jgOhYeah/BikeHorn/Documentation/Images/PCB_Front.jpg

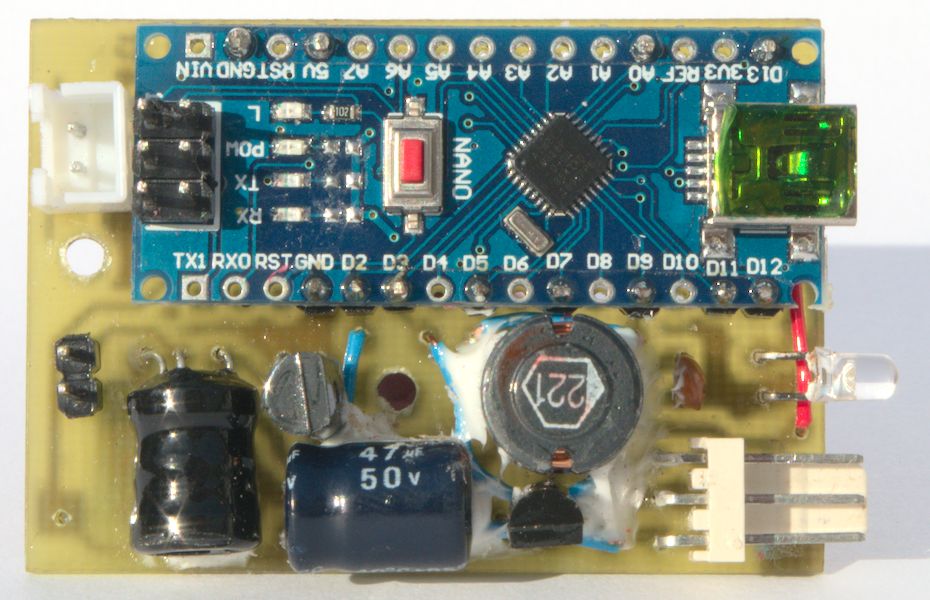
Documentation/Images/PCB_Front.jpg
