jgOhYeah/BikeHorn/Tuning/OptimiserSketch/OptimiserSketch.ino

/**
 * @file OptimiserSketch.ino
 * @author Jotham Gates
 * @brief Sketch for use with the BikeHornOptimiser tool for tuning the horn to get best performance
 * @date 2021-12-30
 * 
 * Upload this sketch to the horn and run BikeHornOptimiser.py.
 * NOTE: This script DOES NOT include any low power features. When you are finished, either remove
 * the batteries or reflash the proper BikeHorn sketch (that does have power saving features),
 * otherwise you will end up with flat batteries.
 */

#include <EEPROM.h>
#include <stdio.h>

#define PIEZO_PIN 9 // Fixed as PB1 (Pin 9 on Arduino Nano)
#define BOOST_PIN 11 // Fixed as PB3 (Pin 11 on Arduino Nano)
#define LED_EXTERNAL 7
#define SERIAL_BAUD 38400

#define VERSION "1.0.0"
#define WELCOME_MSG "Bike horn OPTIMISER V" VERSION " started. Compiled " __TIME__ ", " __DATE__

static FILE uartout = {0}; // https://playground.arduino.cc/Main/Printf/

/**
 * @brief Initial setup and signalling to the computer
 * 
 */
void setup() {
    // Fprintf stuff
    // Fill in the UART file descriptor with pointer to writer.
    fdev_setup_stream (&uartout, uart_putchar, NULL, _FDEV_SETUP_WRITE);
    // The uart is the standard output device STDOUT.
    stdout = &uartout ;

    // Initial setup
    Serial.begin(SERIAL_BAUD);
    Serial.setTimeout(__LONG_MAX__);
    pinMode(LED_BUILTIN, OUTPUT);
    pinMode(LED_EXTERNAL, OUTPUT);
    pinMode(PIEZO_PIN, OUTPUT);
    pinMode(BOOST_PIN, OUTPUT);
    digitalWrite(LED_BUILTIN, HIGH);
    digitalWrite(LED_EXTERNAL, HIGH);
    Serial.println(F(WELCOME_MSG));

    // Wait for the computer
    Serial.println(F("~`~`Ready`~`~"));
}

/**
 * @brief Main program loop
 * 
 */
void loop() {
    // Wait for the start of the message
    digitalWrite(LED_EXTERNAL, HIGH);
    Serial.find("~`~`");
    while(!Serial.available());
    char instruction = Serial.read();
    digitalWrite(LED_EXTERNAL, LOW);

    bool simpleAck = true;

    // Tune playing settings
    uint16_t t1Top, t1Compare;
    uint8_t t2Compare;

    // Interpret the instruction
    switch(instruction) {
        case 'p':
            // Play a note
            t1Top = Serial.parseInt();
            Serial.find('~');
            t1Compare = Serial.parseInt();
            Serial.find('~');
            t2Compare = Serial.parseInt();

            playNote(t1Top, t1Compare, t2Compare);
            break;
        case 's':
            // Stop all timers and noise
            stop();
            break;
        case 'w':
            // Write a eeprom bytes
            writeStream();
            simpleAck = false;
            break;
        case 'r':
            // Read the specified number of eeprom bytes from an address
            dumpEEPROM();
            
    }

    // Acknowledge
    if(simpleAck) {
        // Wait for the end of the message
        Serial.find("`~`~");
        Serial.println(F("~`~`Ack`~`~"));
    }
}

/**
 * @brief Sets up the timers to play with the given parameters
 * 
 * @param t1Top timer 1 top, to be put in ICR1
 * @param t1Compare timer 1 compare, to be put in OCR1A
 * @param t2Compare timer 2 compare, to be put in OCR2A (top is fixed at 0xff)
 */
void playNote(uint16_t t1Top, uint16_t t1Compare, uint8_t t2Compare) {
    // Setup non inverting mode (duty cycle is sensible), fast pwm mode 14 on PB1 (Pin 9)
    TCCR1A = (1 << COM1A1) | (1 << WGM11);
    TCCR1B = (1 << WGM12) | (1 << WGM13) | (1 << CS11); // With prescalar 8 (with a clock frequency of 16MHz, can get all notes required)
    ICR1 = t1Top; // Calculate the corresponding counter
    OCR1A = t1Compare; // Duty cycle

    TCCR2A = (1 << COM2A1) | (1 << WGM21) | (1 << WGM20); // Mode 3, fast PWM, reset at 255
    TCCR2B = (1<< CS20); // Prescalar 1
    OCR2A = t2Compare; // Duty cycle
}

/**
 * @brief Shuts down the timers and stops making noise
 * 
 */
void stop() {
    TCCR1A = 0;
    TCCR1B = 0;
    TCCR2A = 0;
    TCCR2B = 0;

    digitalWrite(BOOST_PIN, LOW);
    digitalWrite(PIEZO_PIN, LOW);
}

void writeStream() {
    uint16_t address = Serial.parseInt();
    bool done = false;
    while(!done) {
        char input = waitByte();
        if(input == '~') {
            // Get and write a byte
            uint8_t data = Serial.parseInt();
            EEPROM.update(address, data);
            address++;
            Serial.println(F("~`~`W`~`~"));
        } else if(input == '`') {
            input = waitByte();
            if(input == '~') {
                input = waitByte();
                if(input == '`') {
                    input = waitByte();
                    if(input == '~') {
                        done = true;
                    }
                }
            }
        }
    }
    Serial.println(F("~`~`Ack`~`~"));
}

char waitByte() {
    while(!Serial.available()) {}
    return Serial.read();
}


void dumpEEPROM() {
    const char WIDTH = 16;
    const int EEPROM_SIZE = 1024;

    // Header row
    printf("     | ");
    for(int i = 0; i < WIDTH; i++) {
        printf("%02X ", i);
    }
    printf("\n");
    for(int i = 0; i < WIDTH*3+7; i++) {
        printf("-", i);
    }

    // Body
    for(int i = 0; i < EEPROM_SIZE; i += WIDTH) {
        printf("\n%04X | ", i);
        // Row
        for(int j = 0; j < WIDTH; j++) {
            printf("%02X ", EEPROM.read(i+j));
        }
    }
    printf("\n");
}

/**
 * @brief output function for printf
 * From https://playground.arduino.cc/Main/Printf/
 * 
 */
static int uart_putchar (char c, FILE *stream) {
    Serial.write(c) ;
    return 0 ;
}
