jgOhYeah/BikeHorn/BikeHorn/tunes.h

/** tunes.h
 * Saved tunes for the BikeHorn to play. Add each tune as an array, then edit
 * the tunes array at the bottom to include the name of the tune.
 * 
 * For more details, see README.md or go to
 * https://github.com/jgOhYeah/BikeHorn
 * 
 * Written by Jotham Gates. Tunes converted from various sources.
 * Last modified 11/01/2021
 */
#pragma once

// Converted from 'WeWishYouAMerryChristmas' by TunePlayer Musescore plugin V1.8.0
const uint16_t WeWishYouAMerryChristmas[] PROGMEM = {
    0xe0c8, // Tempo change to 200 BPM
    0x6a38,0xba38,0xba18,0x1c18,0xba18,0xaa18,0x8a38,0x8a38,0x8a38,0x1c38,
    0x1c18,0x3c18,0x1c18,0xba18,0xaa38,0x6a38,0x6a38,0x3c38,0x3c18,0x4c18,
    0x3c18,0x1c18,0xba38,0x8a38,0x6a18,0x6a18,0x8a38,0x1c38,0xaa38,0xba78,
    0x6a38,0xba18,0xaa18,0x8a18,0xaa18,0xba18,0x8a18,0xaa78,0xaa38,0xba38,
    0xaa38,0x8a38,0x6a78,0x1c38,0x3c38,0x1c18,0x1c18,0xba18,0xba18,0x6c38,
    0x6a38,0x6a18,0x6a18,0x8a38,0x1c38,0xaa38,0xba0c,0xaa0c,0xba0c,0xaa0c,
    0xba38,
    0xf001 // End of tune. Restart from the beginning.
};

// Converted from 'auld_lang_syne_PNO_orig' by TunePlayer Musescore plugin V1.8.0
const uint16_t auld_lang_syne_PNO_orig[] PROGMEM = {
    0xe0dc, // Tempo change to 220 BPM
    0x9a38,0x2c58,0x2c18,0x2c38,0x6c38,0x4c58,0x2c18,0x4c38,0x6c38,0x2c58,
    0x2c18,0x6c38,0x9c38,0xbcb8,0xbc38,0x9c58,0x6c18,0x6c38,0x2c38,0x4c58,
    0x2c18,0x4c38,0x6c38,0x2c58,0xba18,0xba38,0x9a38,0x2cb8,0xbc38,0x9c58,
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
    0x7a38,0x2a18,0x7a38,0x2a38,0x1a18,0x2a38,0x5a38,0x5a3c,0x5a18,0x2a18,
    0xa38,0xa858,0x7898,0x7878,0xa878,0x2a78,0x5a78,0x8a38,0x7a38,0x1a18,
    0x2a38,0xa81c,0xa8f8,
    0xf001 // End of tune. Restart from the beginning.
};

// Converted from 'TakeOnMeIntroLoop' by TunePlayer Musescore plugin V1.7.0
const uint16_t TakeOnMeIntroLoop[] PROGMEM = {
    0xe0c8, // Tempo change to 200 BPM
    0x6a18,0x6a18,0x2a18,0xb838,0xb838,0x4a38,0x4a38,0x4a18,0x8a18,0x8a18,
    0x9a18,0xba18,0x9a18,0x9a18,0x9a18,0x4a38,0x2a38,0x6a38,0x6a38,0x6a18,
    0x4a18,0x4a18,0x6a18,0x4a18,
    0xf001 // End of tune. Restart from the beginning
};

// Converted from 'BlueBikeHorn' by TunePlayer Musescore plugin V1.8.0
const uint16_t BlueBikeHorn[] PROGMEM = {
    0xe0b4, // Tempo change to 180 BPM
    0x9a18,0x1a18,0x6a18,0x9a18,0xba18,0x4a18,0x8a18,0x9a38,0x6a18,0x9a18,
    0x1c18,0x2c18,0x6a18,0x1c18,0xba18,
    0xd410, // Repeat going back 16 notes, repeating 2 time(s)
    0x9a18,0x1a18,0x6a18,0x9a18,0x8a18,0xb818,0x4a18,0x6a38,0x9818,0x4a18,
    0x6a38,0x4a18,0x6a18,0x8a18,
    0xf001 // End of tune. Restart from the beginning.
};

// Burgler alarm tune
// Converted from 'BabyShark' by TunePlayer Musescore plugin V1.8.1
const uint16_t babyShark[] PROGMEM = {
    0xe0b4, // Tempo change to 180 BPM
    0x4a38,0x6a38,0x9a18,0x9a08,0x9a00,0x9a08,0x9a08,0x9a18,0x9a08,0x9a18,
    0x4a18,0x6a18,0x9a18,0x9a08,0x9a00,0x9a08,0x9a08,0x9a18,0x9a08,0x9a18,
    0x4a18,0x6a18,0x9a18,0x9a08,0x9a00,0x9a08,0x9a08,0x9a18,0x9a08,0x9a18,
    0x9a18,0x9a18,0x8a3a,0xc038,
    0xd823, // Repeat going back 35 notes, repeating 3 time(s)
    0x4a78,0x6a78,0x9af8,
    0xf000 // End of tune. Stop playing.
};

const uint16_t *const tunes[] PROGMEM = {WeWishYouAMerryChristmas, auld_lang_syne_PNO_orig, rossini_william_tell, BlueBikeHorn, TakeOnMeIntroLoop, ImperialMarchPICAXE, FinalCountdownLow, FinalCountdownHigh, Cantina, beep, beepHigh};
const uint8_t tuneCount = sizeof(tunes) / sizeof(uint16_t);

#define BURGLER_ALARM_TUNE babyShark
